Brezensalzer/ESP32_Web_Radio_I2S/philco_45c/IMG_1976.JPG

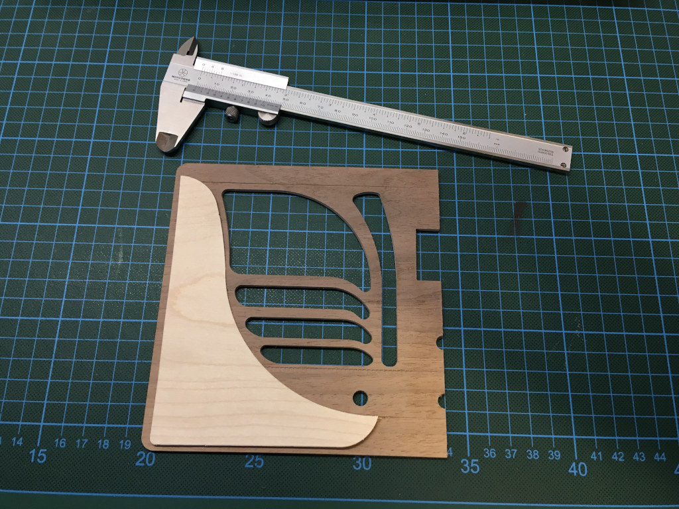
philco_45c/IMG_1976.JPG
