Brezensalzer/ESP32_Web_Radio_I2S/philco_45c/IMG_2015.JPG

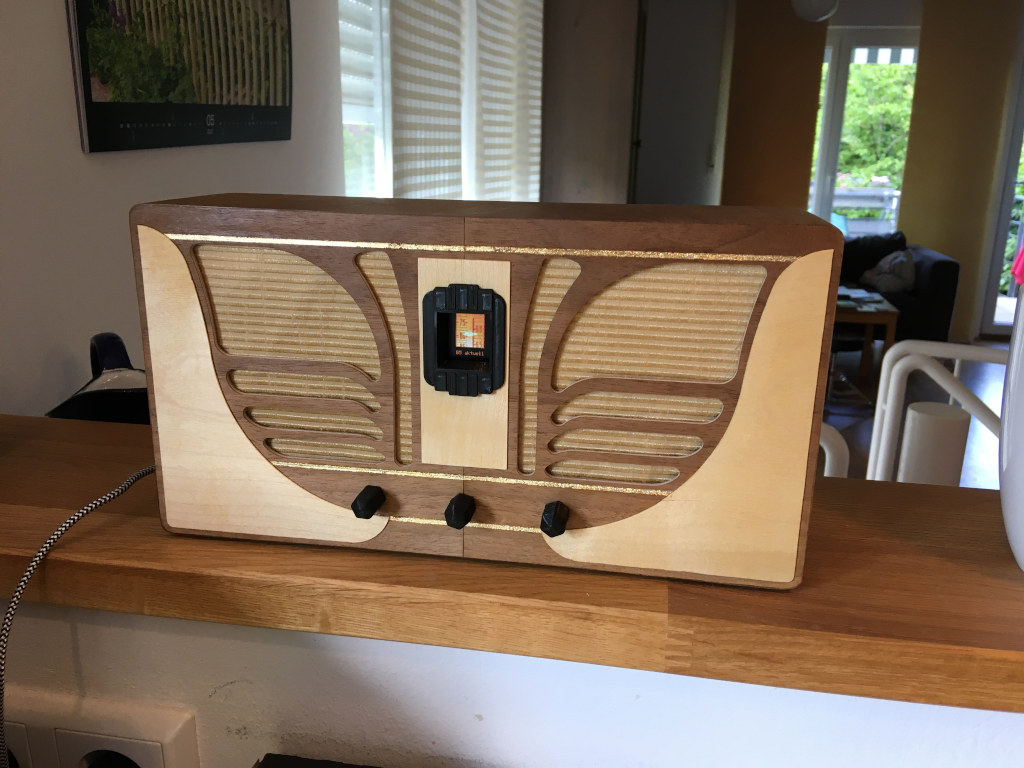
philco_45c/IMG_2015.JPG
