Brezensalzer/ESP32_Web_Radio_I2S/philco_45c/IMG_2021.JPG

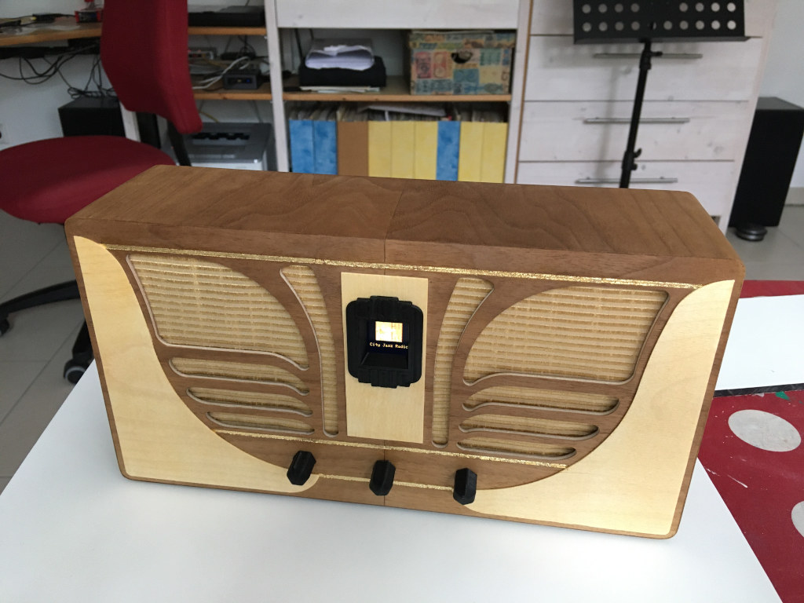
philco_45c/IMG_2021.JPG
