Brezensalzer/ESP32_Web_Radio_I2S/config.h

/*
 * config.h
 * credentials
 */
 
//------------------------------------------------------------------------------
// Network
//------------------------------------------------------------------------------
// your network SSID (name)
char ssid[] = "<WiFi SSID>";             
// your network password
char pass[] = "<password>";   
// URL to station list
char url_stationlist[] = "http://<hostname>/stationlist_philco.txt";
